osptek/tft-4.3-480x800-mipi-st7102/versions/YDP430BT009-V1/examples/rpi5-lvgl-st7102-st7123-480x800/st7123_touch.c

// SPDX-License-Identifier: GPL-2.0
/*
 * Sitronix ST7123 Touchscreen Driver
 * Compatible with Raspberry Pi 5 + vc4-kms-dsi-st7102-st7123.dts
 *
 * This example is from the open-source sharing by engineers of Yuying Optoelectronics (鱼鹰光电)
 * on Github.com/osptek. Welcome to provide improvement suggestions.
 *
 * 本例程来源于鱼鹰光电的工程师的开源分享 Github.com/osptek，欢迎提出改进意见
 */

#include <linux/delay.h>
#include <linux/gpio/consumer.h>
#include <linux/i2c.h>
#include <linux/input.h>
#include <linux/input/mt.h>
#include <linux/input/touchscreen.h>
#include <linux/interrupt.h>
#include <linux/module.h>
#include <linux/slab.h>

#define ST7123_TS_NAME			"st7123"

#define ST7123_STATUS_REG		0x0001
#define ST7123_DEVICE_CONTROL_REG	0x0002
#define ST7123_X_RESOLUTION_HIGH	0x0005
#define ST7123_MAX_NUM_TOUCHES		0x0009
#define ST7123_TOUCH_INFO		0x0010
#define ST7123_MISC_INFO		0x00f0
#define ST7123_CHIP_ID			0x00f4

#define ST7123_CHIP_ID_VALUE		0x83
#define ST7123_MISC_COORD_CHKSUM	BIT(4)
#define ST7123_MAX_SUPPORTED_TOUCHES	10
#define ST7123_DEFAULT_MAX_TOUCHES	5
#define ST7123_DEFAULT_X_RES		480
#define ST7123_DEFAULT_Y_RES		800
#define ST7123_POLL_INTERVAL_MS		17
#define ST7123_TOUCH_STRIDE		7
#define ST7123_TOUCH_HEADER_LEN		4
#define ST7123_CHECKSUM_SEED		0x5a

struct st7123_ts_data {
	struct i2c_client *client;
	struct input_dev *input;
	struct gpio_desc *reset_gpio;
	struct touchscreen_properties prop;
	struct mutex lock;
	char name[64];
	u8 max_touches;
	bool has_coord_checksum;
	bool suspended;
	u8 coord_buf[ST7123_TOUCH_HEADER_LEN +
		     ST7123_MAX_SUPPORTED_TOUCHES * ST7123_TOUCH_STRIDE + 1];
};

static int st7123_read(struct st7123_ts_data *ts, u16 reg, void *buf, u16 len)
{
	struct i2c_client *client = ts->client;
	u8 addr[2] = { reg >> 8, reg & 0xff };
	struct i2c_msg msg[] = {
		{
			.addr = client->addr,
			.len  = sizeof(addr),
			.buf  = addr,
		},
		{
			.addr  = client->addr,
			.flags = I2C_M_RD,
			.len   = len,
			.buf   = buf,
		},
	};
	int ret;

	ret = i2c_transfer(client->adapter, msg, ARRAY_SIZE(msg));
	if (ret != ARRAY_SIZE(msg))
		return ret < 0 ? ret : -EIO;

	return 0;
}

static int st7123_write(struct st7123_ts_data *ts, u16 reg, const void *buf,
			u16 len)
{
	struct i2c_client *client = ts->client;
	u8 *data;
	int ret;

	data = kmalloc(len + 2, GFP_KERNEL);
	if (!data)
		return -ENOMEM;

	data[0] = reg >> 8;
	data[1] = reg & 0xff;
	memcpy(&data[2], buf, len);

	ret = i2c_master_send(client, data, len + 2);
	kfree(data);

	if (ret != len + 2)
		return ret < 0 ? ret : -EIO;

	return 0;
}

static u8 st7123_checksum(const u8 *buf, int len)
{
	u16 checksum = ST7123_CHECKSUM_SEED;
	u8 low;
	int i;

	for (i = 0; i < len; i++) {
		checksum += buf[i];
		low = checksum & 0xff;
		low = (low >> 7) | (low << 1);
		checksum = (checksum & 0xff00) | low;
	}

	return checksum & 0xff;
}

static void st7123_reset(struct st7123_ts_data *ts)
{
	if (!ts->reset_gpio)
		return;

	gpiod_set_value_cansleep(ts->reset_gpio, 1);
	fsleep(10000);
	gpiod_set_value_cansleep(ts->reset_gpio, 0);
	msleep(150);
}

static int st7123_read_resolution(struct st7123_ts_data *ts, u16 *x, u16 *y)
{
	u8 buf[4];
	int ret;

	ret = st7123_read(ts, ST7123_X_RESOLUTION_HIGH, buf, sizeof(buf));
	if (ret)
		return ret;

	*x = ((buf[0] & 0x3f) << 8) | buf[1];
	*y = ((buf[2] & 0x3f) << 8) | buf[3];

	if (!*x || !*y)
		return -EINVAL;

	return 0;
}

static int st7123_read_max_touches(struct st7123_ts_data *ts)
{
	u8 max_touches;
	int ret;

	ret = st7123_read(ts, ST7123_MAX_NUM_TOUCHES, &max_touches,
			  sizeof(max_touches));
	if (ret)
		return ret;

	if (!max_touches || max_touches > ST7123_MAX_SUPPORTED_TOUCHES)
		max_touches = ST7123_DEFAULT_MAX_TOUCHES;

	ts->max_touches = max_touches;
	return 0;
}

static int st7123_read_misc_info(struct st7123_ts_data *ts)
{
	u8 misc;
	int ret;

	ret = st7123_read(ts, ST7123_MISC_INFO, &misc, sizeof(misc));
	if (ret)
		return ret;

	ts->has_coord_checksum = !!(misc & ST7123_MISC_COORD_CHKSUM);
	return 0;
}

static int st7123_check_id(struct st7123_ts_data *ts)
{
	struct device *dev = &ts->client->dev;
	u8 chip_id;
	int ret;

	ret = st7123_read(ts, ST7123_CHIP_ID, &chip_id, sizeof(chip_id));
	if (ret)
		return ret;

	if (chip_id != ST7123_CHIP_ID_VALUE)
		dev_warn(dev, "unexpected chip id 0x%02x (expected 0x%02x)\n",
			 chip_id, ST7123_CHIP_ID_VALUE);

	return 0;
}

static int st7123_wait_ready(struct st7123_ts_data *ts)
{
	u8 status;
	int ret;
	int i;

	for (i = 0; i < 100; i++) {
		ret = st7123_read(ts, ST7123_STATUS_REG, &status, sizeof(status));
		if (!ret && ((status & 0x0f) == 0x00 || (status & 0x0f) == 0x04))
			return 0;
		usleep_range(1000, 2000);
	}

	return ret ?: -ETIMEDOUT;
}

static void st7123_report_all_up(struct st7123_ts_data *ts)
{
	int i;

	for (i = 0; i < ts->max_touches; i++) {
		input_mt_slot(ts->input, i);
		input_mt_report_slot_state(ts->input, MT_TOOL_FINGER, false);
	}

	input_mt_sync_frame(ts->input);
	input_sync(ts->input);
}

static int st7123_report_touch_data(struct st7123_ts_data *ts)
{
	struct device *dev = &ts->client->dev;
	int read_len;
	int ret;
	int i;

	read_len = ST7123_TOUCH_HEADER_LEN +
		   ts->max_touches * ST7123_TOUCH_STRIDE;
	if (ts->has_coord_checksum)
		read_len++;

	ret = st7123_read(ts, ST7123_TOUCH_INFO, ts->coord_buf, read_len);
	if (ret) {
		dev_warn_ratelimited(dev, "failed to read touch data: %d\n", ret);
		return ret;
	}

	/* Bit7 of first byte requests controller reset */
	if (ts->coord_buf[0] & BIT(7)) {
		dev_warn(dev, "controller requested reset\n");
		st7123_report_all_up(ts);
		st7123_reset(ts);
		return -EIO;
	}

	if (ts->has_coord_checksum) {
		u8 checksum = st7123_checksum(ts->coord_buf, read_len - 1);
		if (checksum != ts->coord_buf[read_len - 1]) {
			dev_warn_ratelimited(dev, "touch checksum mismatch\n");
			return -EIO;
		}
	}

	for (i = 0; i < ts->max_touches; i++) {
		u8 *p = &ts->coord_buf[ST7123_TOUCH_HEADER_LEN +
				       i * ST7123_TOUCH_STRIDE];
		u16 x, y;

		input_mt_slot(ts->input, i);

		if (!(p[0] & BIT(7))) {
			input_mt_report_slot_state(ts->input, MT_TOOL_FINGER, false);
			continue;
		}

		x = ((p[0] & 0x3f) << 8) | p[1];
		y = ((p[2] & 0x3f) << 8) | p[3];

		input_mt_report_slot_state(ts->input, MT_TOOL_FINGER, true);
		touchscreen_report_pos(ts->input, &ts->prop, x, y, true);
		input_report_abs(ts->input, ABS_MT_TOUCH_MAJOR, max_t(u8, p[4], 1));
	}

	input_mt_sync_frame(ts->input);
	input_sync(ts->input);

	return 0;
}

static void st7123_poll(struct input_dev *input)
{
	struct st7123_ts_data *ts = input_get_drvdata(input);

	mutex_lock(&ts->lock);
	if (!ts->suspended)
		st7123_report_touch_data(ts);
	mutex_unlock(&ts->lock);
}

static irqreturn_t st7123_irq_thread(int irq, void *dev_id)
{
	struct st7123_ts_data *ts = dev_id;

	mutex_lock(&ts->lock);
	if (!ts->suspended)
		st7123_report_touch_data(ts);
	mutex_unlock(&ts->lock);

	return IRQ_HANDLED;
}

static int st7123_powerdown(struct st7123_ts_data *ts, bool powerdown)
{
	u8 ctrl;
	int ret;

	ret = st7123_read(ts, ST7123_DEVICE_CONTROL_REG, &ctrl, sizeof(ctrl));
	if (ret)
		return ret;

	if (powerdown)
		ctrl |= BIT(1);
	else
		ctrl &= ~BIT(1);

	return st7123_write(ts, ST7123_DEVICE_CONTROL_REG, &ctrl, sizeof(ctrl));
}

static int st7123_probe(struct i2c_client *client)
{
	struct device *dev = &client->dev;
	struct st7123_ts_data *ts;
	struct input_dev *input;
	u16 max_x = ST7123_DEFAULT_X_RES;
	u16 max_y = ST7123_DEFAULT_Y_RES;
	int ret;

	if (!i2c_check_functionality(client->adapter, I2C_FUNC_I2C))
		return dev_err_probe(dev, -EIO, "I2C transfers not supported\n");

	ts = devm_kzalloc(dev, sizeof(*ts), GFP_KERNEL);
	if (!ts)
		return -ENOMEM;

	input = devm_input_allocate_device(dev);
	if (!input)
		return -ENOMEM;

	ts->client = client;
	ts->input = input;
	ts->max_touches = ST7123_DEFAULT_MAX_TOUCHES;
	mutex_init(&ts->lock);
	i2c_set_clientdata(client, ts);

	/* Optional reset GPIO (commented out in DTS) */
	ts->reset_gpio = devm_gpiod_get_optional(dev, "reset", GPIOD_OUT_LOW);
	if (IS_ERR(ts->reset_gpio))
		return dev_err_probe(dev, PTR_ERR(ts->reset_gpio),
				     "failed to request reset GPIO\n");

	st7123_reset(ts);

	ret = st7123_wait_ready(ts);
	if (ret)
		return dev_err_probe(dev, ret, "controller not ready\n");

	ret = st7123_check_id(ts);
	if (ret)
		return dev_err_probe(dev, ret, "failed to read chip id\n");

	ret = st7123_read_resolution(ts, &max_x, &max_y);
	if (ret)
		dev_warn(dev, "using default resolution %ux%u\n", max_x, max_y);

	ret = st7123_read_max_touches(ts);
	if (ret)
		dev_warn(dev, "using default max touches %u\n", ts->max_touches);

	ret = st7123_read_misc_info(ts);
	if (ret)
		dev_warn(dev, "failed to read misc info: %d\n", ret);

	snprintf(ts->name, sizeof(ts->name), "%s Sitronix ST7123 Touchscreen",
		 dev_name(dev));
	input->name = ts->name;
	input->id.bustype = BUS_I2C;
	input->dev.parent = dev;
	input_set_drvdata(input, ts);

	/* Absolute parameters – will be overridden by DTS touchscreen-size-* */
	input_set_abs_params(input, ABS_MT_POSITION_X, 0, max_x - 1, 0, 0);
	input_set_abs_params(input, ABS_MT_POSITION_Y, 0, max_y - 1, 0, 0);
	input_set_abs_params(input, ABS_MT_TOUCH_MAJOR, 0, 255, 0, 0);

	/* Parse DTS properties (touchscreen-size-x/y, inverted, swapped, etc.) */
	touchscreen_parse_properties(input, true, &ts->prop);

	ret = input_mt_init_slots(input, ts->max_touches,
				  INPUT_MT_DIRECT | INPUT_MT_DROP_UNUSED);
	if (ret)
		return dev_err_probe(dev, ret, "failed to initialize MT slots\n");

	/* Prefer IRQ if present in DTS, otherwise fall back to polling */
	if (client->irq > 0) {
		ret = devm_request_threaded_irq(dev, client->irq, NULL,
						st7123_irq_thread,
						IRQF_ONESHOT | IRQF_TRIGGER_FALLING,
						client->name, ts);
		if (ret)
			return dev_err_probe(dev, ret, "failed to request IRQ\n");
		dev_info(dev, "using interrupt mode (IRQ %d)\n", client->irq);
	} else {
		ret = input_setup_polling(input, st7123_poll);
		if (ret)
			return dev_err_probe(dev, ret, "failed to set up polling\n");

		input_set_poll_interval(input, ST7123_POLL_INTERVAL_MS);
		dev_info(dev, "using polling mode (%d ms)\n", ST7123_POLL_INTERVAL_MS);
	}

	ret = input_register_device(input);
	if (ret)
		return dev_err_probe(dev, ret, "failed to register input device\n");

	dev_info(dev, "ST7123 touchscreen registered (max_touches=%u)\n",
		 ts->max_touches);

	return 0;
}

static int st7123_suspend(struct device *dev)
{
	struct i2c_client *client = to_i2c_client(dev);
	struct st7123_ts_data *ts = i2c_get_clientdata(client);
	bool wakeup = device_may_wakeup(dev);

	if (client->irq) {
		if (wakeup)
			enable_irq_wake(client->irq);
		else
			disable_irq(client->irq);
	}

	mutex_lock(&ts->lock);
	ts->suspended = true;
	st7123_report_all_up(ts);
	if (!wakeup)
		st7123_powerdown(ts, true);
	mutex_unlock(&ts->lock);

	return 0;
}

static int st7123_resume(struct device *dev)
{
	struct i2c_client *client = to_i2c_client(dev);
	struct st7123_ts_data *ts = i2c_get_clientdata(client);
	bool wakeup = device_may_wakeup(dev);

	mutex_lock(&ts->lock);
	if (!wakeup) {
		st7123_powerdown(ts, false);
		st7123_reset(ts);
	}
	ts->suspended = false;
	mutex_unlock(&ts->lock);

	if (client->irq) {
		if (wakeup)
			disable_irq_wake(client->irq);
		else
			enable_irq(client->irq);
	}

	return 0;
}

static DEFINE_SIMPLE_DEV_PM_OPS(st7123_pm_ops, st7123_suspend, st7123_resume);

static const struct i2c_device_id st7123_id[] = {
	{ "st7123", 0 },
	{ }
};
MODULE_DEVICE_TABLE(i2c, st7123_id);

static const struct of_device_id st7123_of_match[] = {
	{ .compatible = "sitronix,st7123" },
	{ }
};
MODULE_DEVICE_TABLE(of, st7123_of_match);

static struct i2c_driver st7123_driver = {
	.probe    = st7123_probe,
	.id_table = st7123_id,
	.driver = {
		.name           = ST7123_TS_NAME,
		.of_match_table = st7123_of_match,
		.pm             = pm_sleep_ptr(&st7123_pm_ops),
		.probe_type     = PROBE_PREFER_ASYNCHRONOUS,
	},
};
module_i2c_driver(st7123_driver);

MODULE_AUTHOR("Sitronix Technology Co., Ltd.");
MODULE_DESCRIPTION("Sitronix ST7123 Touchscreen Driver");
MODULE_LICENSE("GPL");
